Drmarbles5/Desk-Clock-Timer-Thing/firmware/DCLKTIM_BLE/STM32_WPAN/App/p2p_server_app.c

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

/* Includes ------------------------------------------------------------------*/
#include "main.h"
#include "app_common.h"
#include "dbg_trace.h"
#include "ble.h"
#include "p2p_server_app.h"
#include "stm32_seq.h"

/* USER CODE BEGIN PTD */
typedef struct {
  uint8_t            Led;
} P2P_LedCharValue_t;

typedef struct {
  P2P_LedCharValue_t LedControl;
  uint16_t           ConnectionHandle;
} P2P_Server_App_Context_t;
/* USER CODE END PTD */

/* USER CODE BEGIN PV */
/**
 * START of Section BLE_APP_CONTEXT
 */

static P2P_Server_App_Context_t P2P_Server_App_Context;

/**
 * END of Section BLE_APP_CONTEXT
 */
/* USER CODE END PV */

/* USER CODE BEGIN PFP */
static void P2PS_APP_LED_BUTTON_context_Init(void);
/* USER CODE END PFP */

/* Functions Definition ------------------------------------------------------*/
void P2PS_STM_App_Notification(P2PS_STM_App_Notification_evt_t *pNotification)
{
  switch(pNotification->P2P_Evt_Opcode)
  {
/* USER CODE BEGIN P2PS_STM_App_Notification_P2P_Evt_Opcode */
#if(BLE_CFG_OTA_REBOOT_CHAR != 0)
    case P2PS_STM_BOOT_REQUEST_EVT:
      *(uint32_t*)SRAM1_BASE = *(uint32_t*)pNotification->DataTransfered.pPayload;
      NVIC_SystemReset();
      break;
#endif
/* USER CODE END P2PS_STM_App_Notification_P2P_Evt_Opcode */

    case P2PS_STM__NOTIFY_ENABLED_EVT:
      break;

    case P2PS_STM_NOTIFY_DISABLED_EVT:
      break;

    case P2PS_STM_WRITE_EVT:
/* USER CODE BEGIN P2PS_STM_WRITE_EVT */
      if(pNotification->DataTransfered.pPayload[0] == 0x01)
      {
        HAL_GPIO_WritePin(USR_LED_GPIO_Port, USR_LED_Pin, 1);
        P2P_Server_App_Context.LedControl.Led=0x01; /* LED ON */
      }
      else
      {
        HAL_GPIO_WritePin(USR_LED_GPIO_Port, USR_LED_Pin, 0);
        P2P_Server_App_Context.LedControl.Led=0x00; /* LED OFF */
      }
/* USER CODE END P2PS_STM_WRITE_EVT */
      break;

    default:
/* USER CODE BEGIN P2PS_STM_App_Notification_default */

/* USER CODE END P2PS_STM_App_Notification_default */
      break;
  }
  return;
}

void P2PS_APP_Notification(P2PS_APP_ConnHandle_Not_evt_t *pNotification)
{
  switch(pNotification->P2P_Evt_Opcode)
  {
/* USER CODE BEGIN P2PS_APP_Notification_P2P_Evt_Opcode */

/* USER CODE END P2PS_APP_Notification_P2P_Evt_Opcode */
  case PEER_CONN_HANDLE_EVT :
    break;

    case PEER_DISCON_HANDLE_EVT :
/* USER CODE BEGIN PEER_DISCON_HANDLE_EVT */
       P2PS_APP_LED_BUTTON_context_Init();
/* USER CODE END PEER_DISCON_HANDLE_EVT */
    break;

    default:
      break;
  }
  return;
}

void P2PS_APP_Init(void)
{
/* USER CODE BEGIN P2PS_APP_Init */
  P2PS_APP_LED_BUTTON_context_Init();
/* USER CODE END P2PS_APP_Init */
  return;
}

/* USER CODE BEGIN FD */
void P2PS_APP_LED_BUTTON_context_Init(void){

  HAL_GPIO_WritePin(USR_LED_GPIO_Port, USR_LED_Pin, 0);
  P2P_Server_App_Context.LedControl.Led=0x00; /* led OFF */
}

/* USER CODE END FD */

/*************************************************************
 *
 * LOCAL FUNCTIONS
 *
 *************************************************************/
/* USER CODE BEGIN FD_LOCAL_FUNCTIONS*/

/* USER CODE END FD_LOCAL_FUNCTIONS*/
